tominabox1/Keyboards/leftover30/documents/_image/backlight.jpg

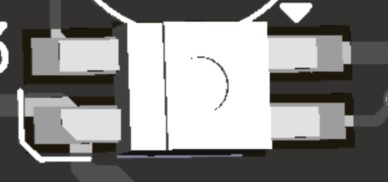
leftover30/documents/_image/backlight.jpg
