tominabox1/Keyboards/leftover30/documents/_image/layout.png

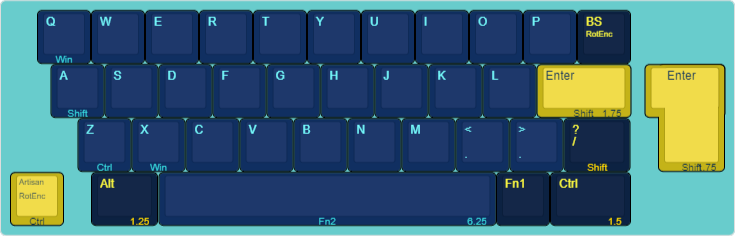
leftover30/documents/_image/layout.png
