tominabox1/Keyboards/leftover30/documents/_image/led2.jpg

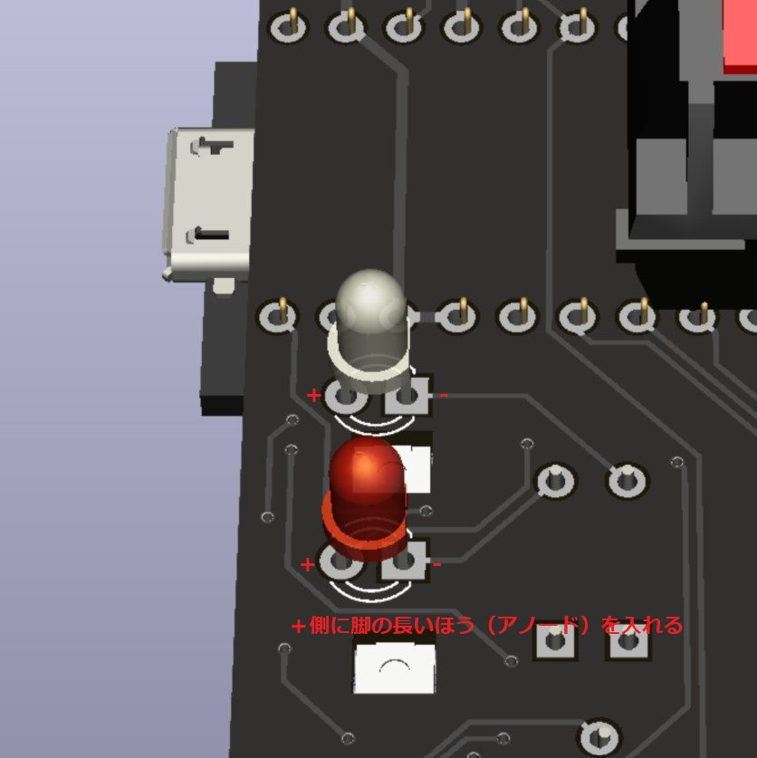
leftover30/documents/_image/led2.jpg
