tominabox1/Keyboards/leftover30/documents/_image/led3.jpg

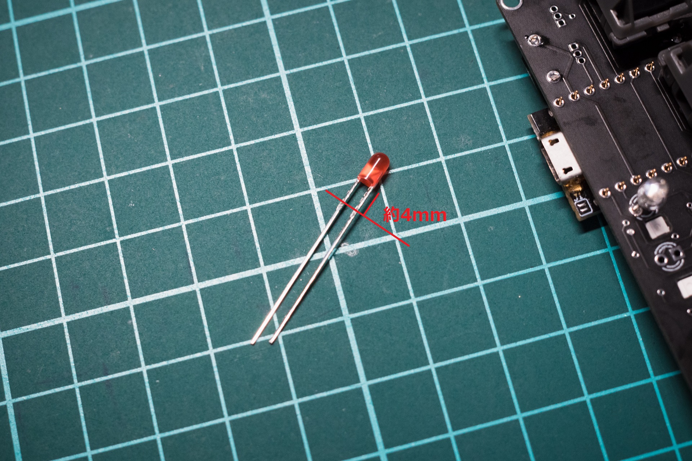
leftover30/documents/_image/led3.jpg
