tominabox1/Keyboards/leftover30/documents/_image/re_cover2.jpg

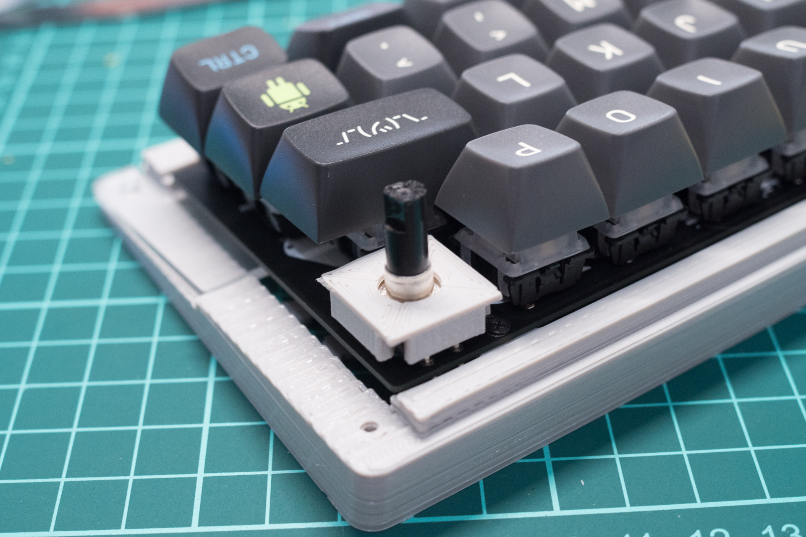
leftover30/documents/_image/re_cover2.jpg
