tominabox1/Keyboards/leftover30/documents/_image/sidegrow.jpg

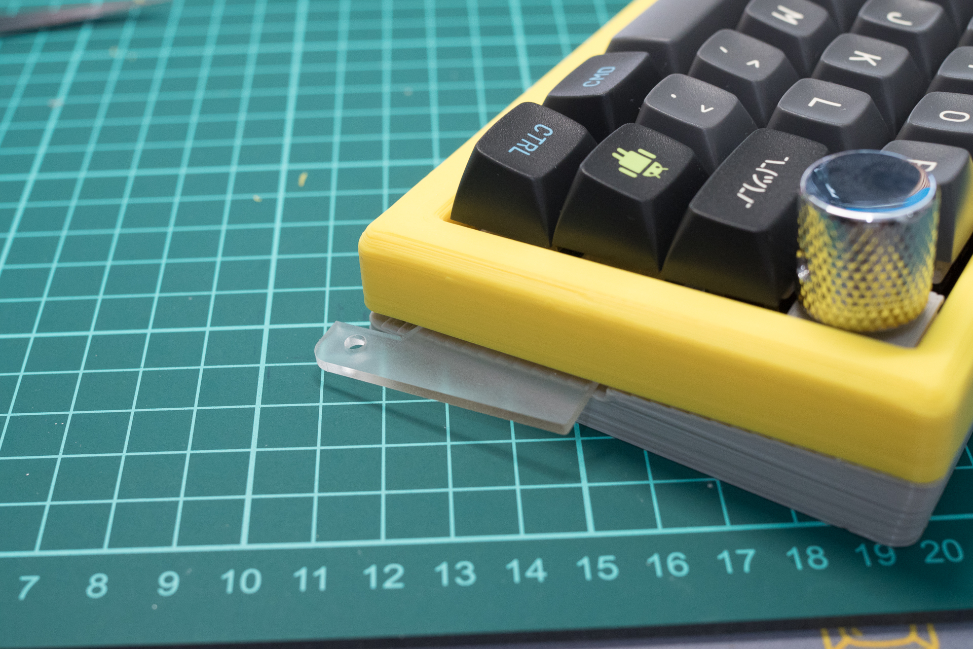
leftover30/documents/_image/sidegrow.jpg
