tominabox1/Keyboards/leftover30/documents/_image/switch.jpg

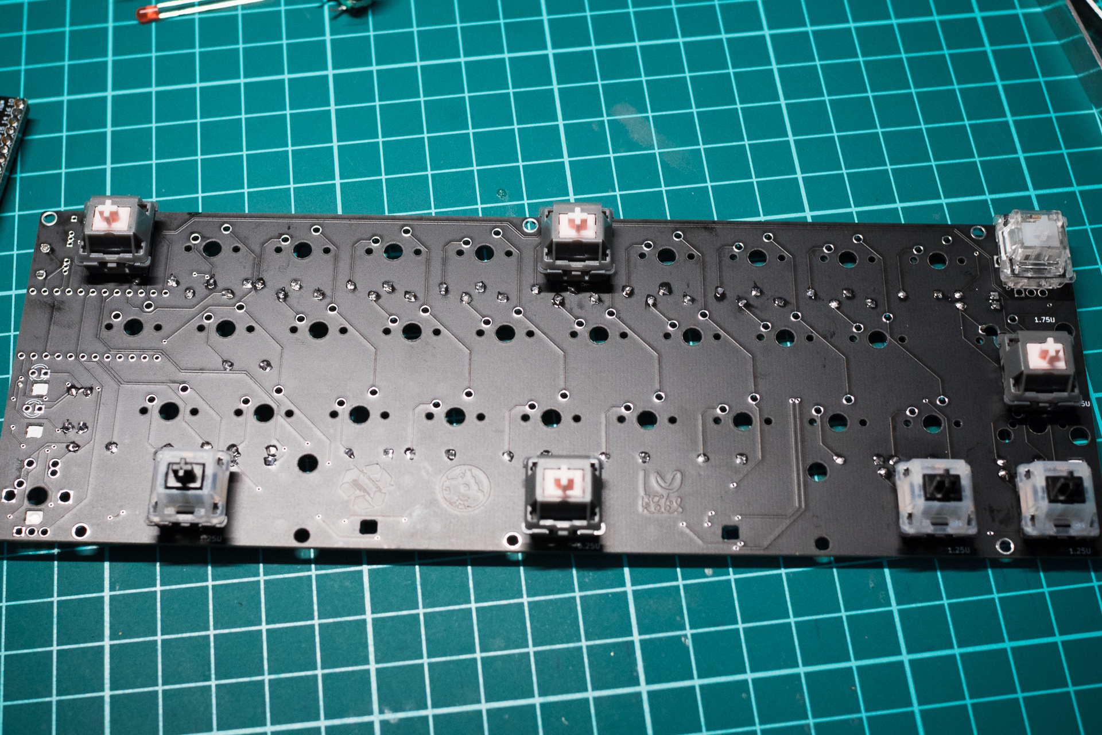
leftover30/documents/_image/switch.jpg
