tominabox1/Keyboards/treadstone32/documents/_image/20200119-P1190029.jpg

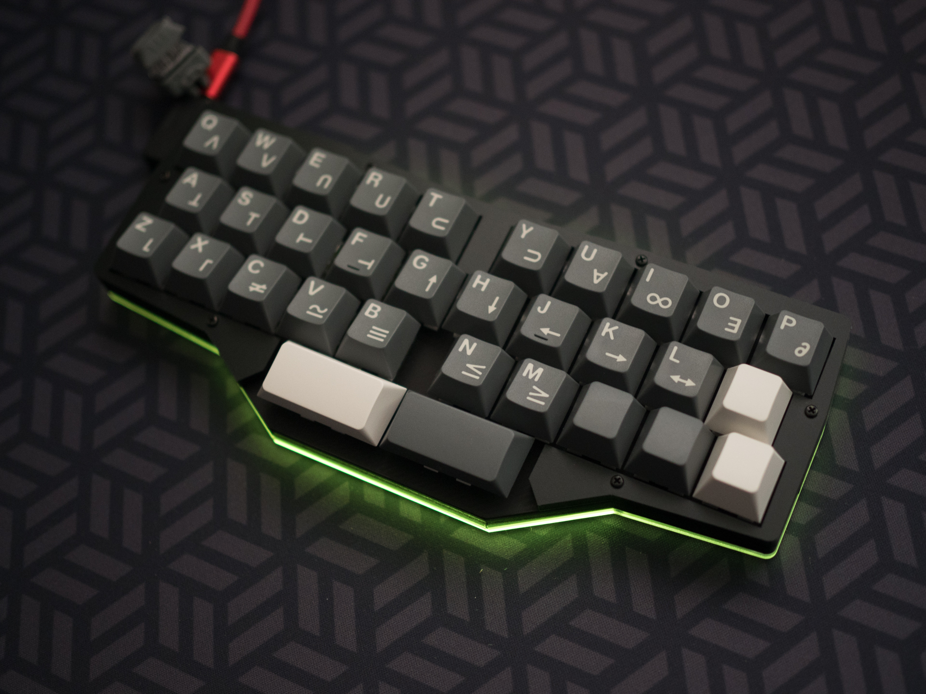
treadstone32/documents/_image/20200119-P1190029.jpg
