tominabox1/Keyboards/treadstone32/documents/_image/20200509-P5090001.jpg

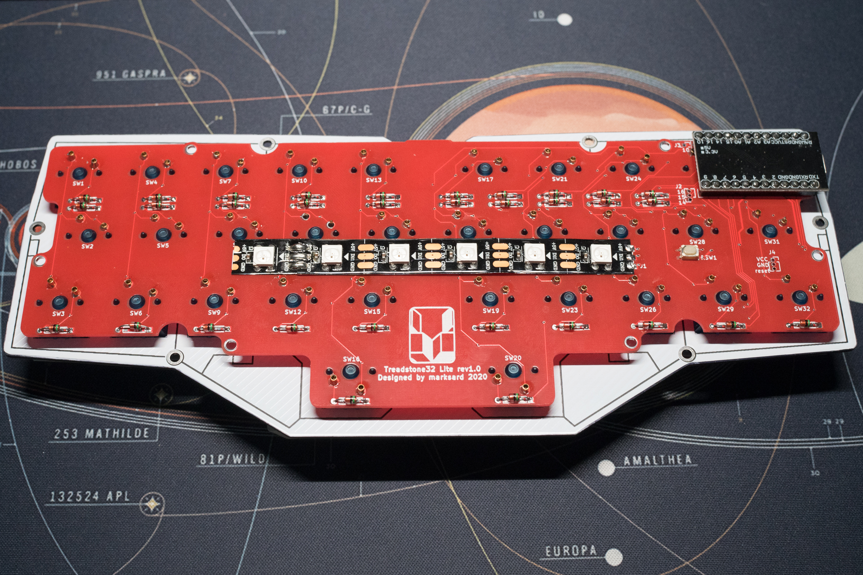
treadstone32/documents/_image/20200509-P5090001.jpg
