tominabox1/Keyboards/treadstone48/documents/_image/20200118-P1180017.jpg

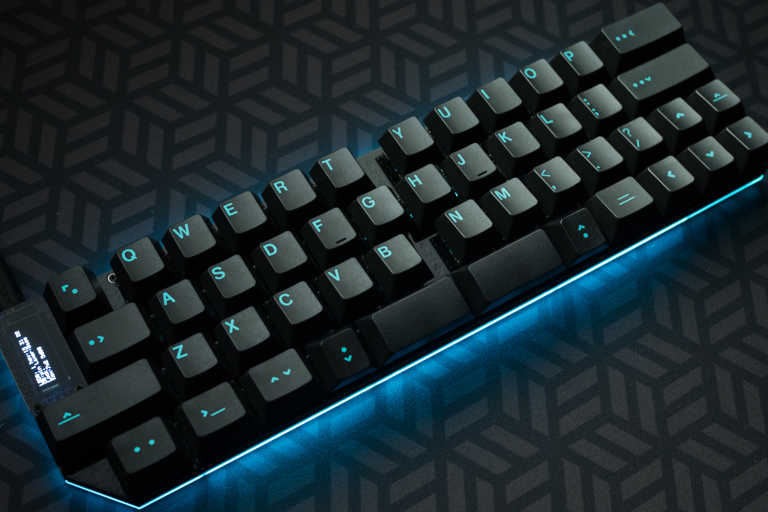
treadstone48/documents/_image/20200118-P1180017.jpg
