tominabox1/Keyboards/treadstone48/documents/_image/20200426-P1010002.jpg

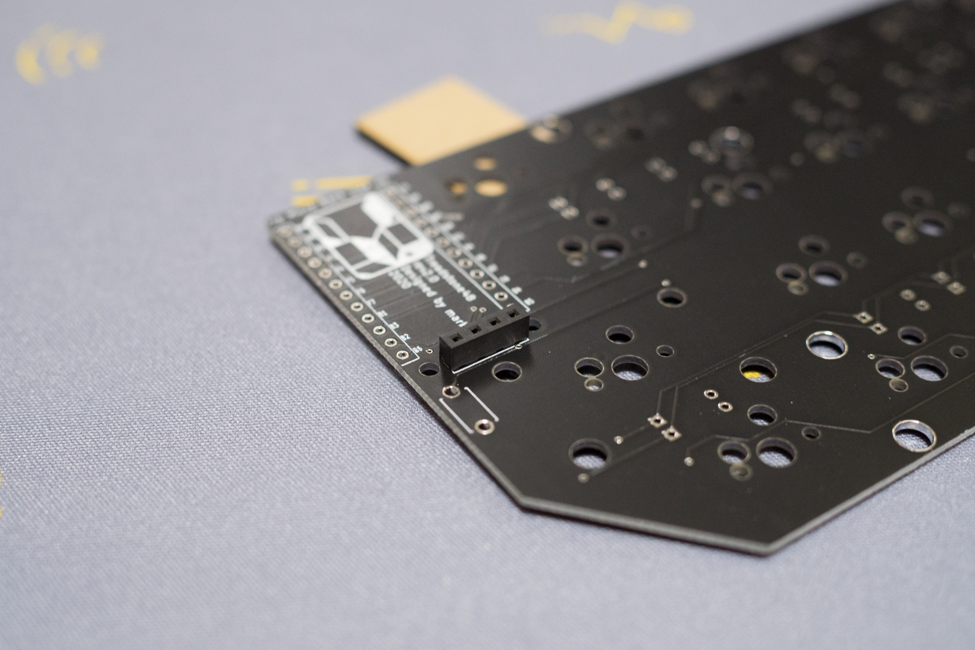
treadstone48/documents/_image/20200426-P1010002.jpg
