tominabox1/Keyboards/treadstone48/documents/_image/20200426-P1010006.jpg

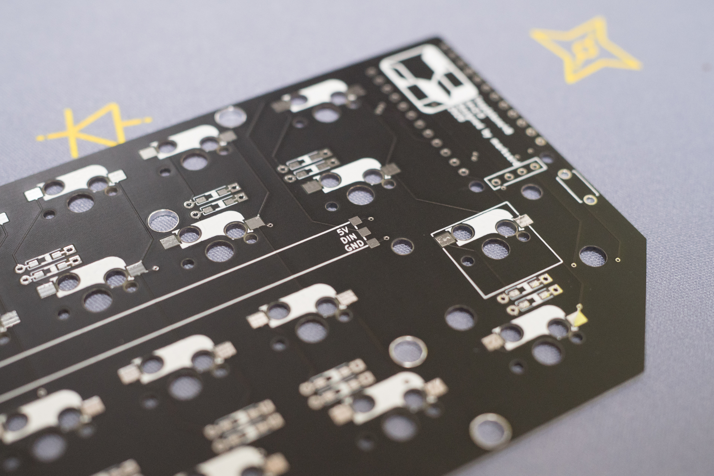
treadstone48/documents/_image/20200426-P1010006.jpg
