tominabox1/Keyboards/treadstone48/documents/_image/20200508-P5080004.jpg

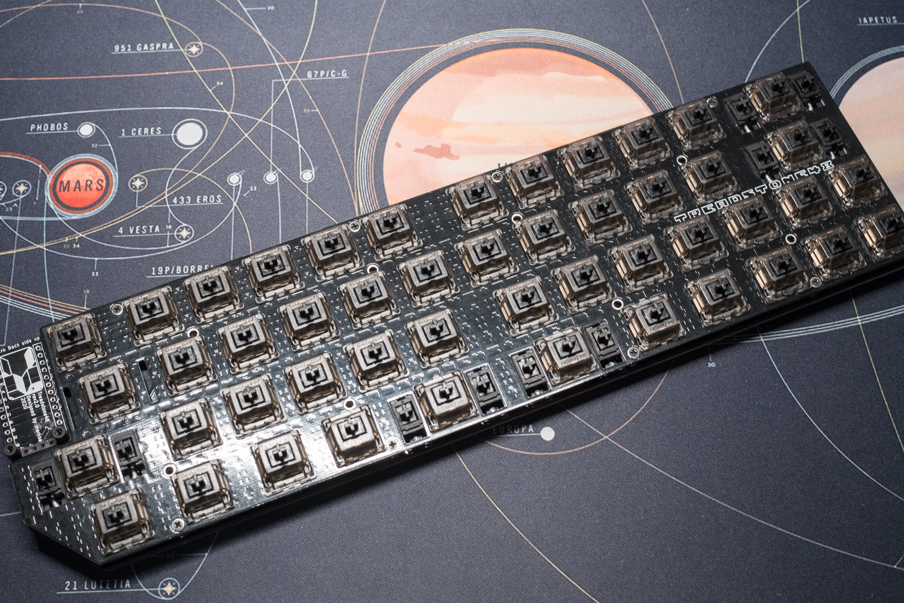
treadstone48/documents/_image/20200508-P5080004.jpg
