tominabox1/Keyboards/treadstone60/documents/_image/hkey_socket2.jpg

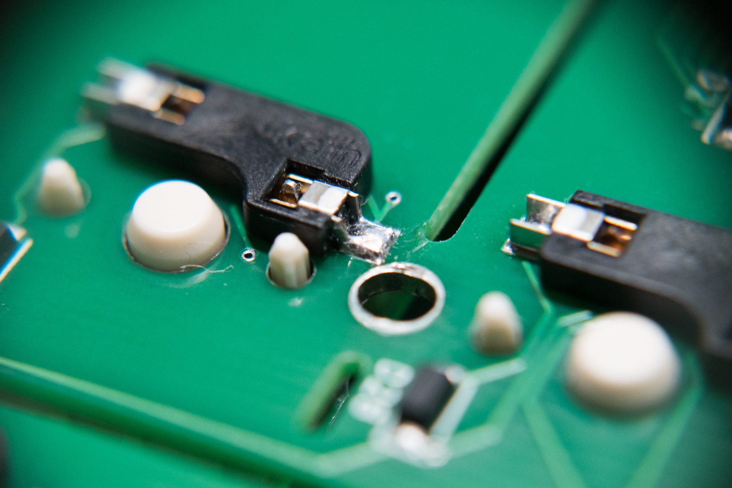
treadstone60/documents/_image/hkey_socket2.jpg
