tominabox1/Keyboards/treadstone60/documents/_image/keymap.png

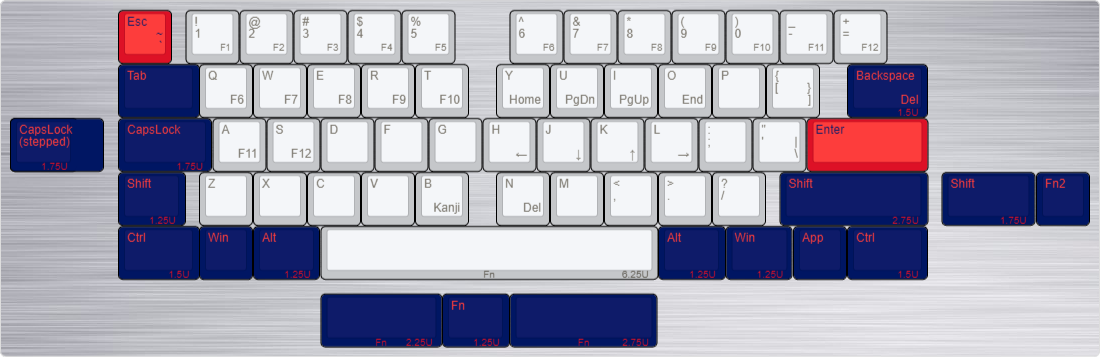
treadstone60/documents/_image/keymap.png
